7-the-group/1st-semester-project/Hardware/3D_model/Walls_model/walls2.jpg

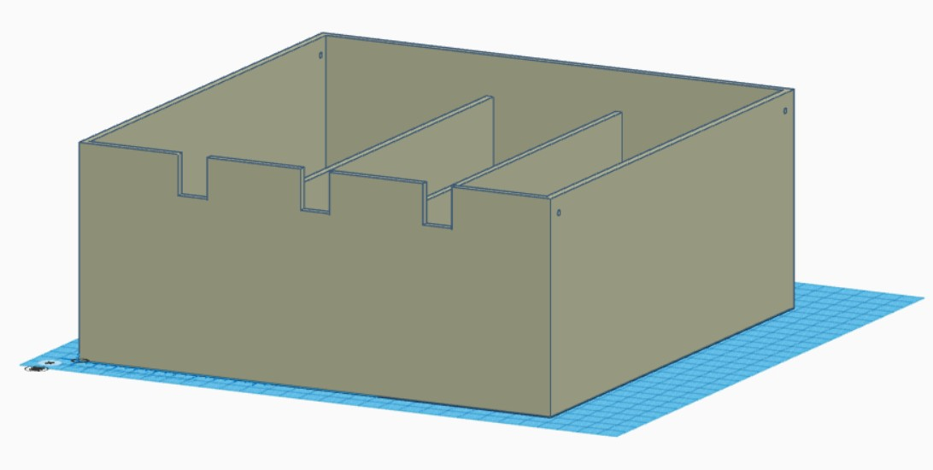
Hardware/3D_model/Walls_model/walls2.jpg
