7-the-group/1st-semester-project/Hardware/Schematic_and_PCB/Control panel (LCD and buttons)/LCD/LCD_sketch.jpg

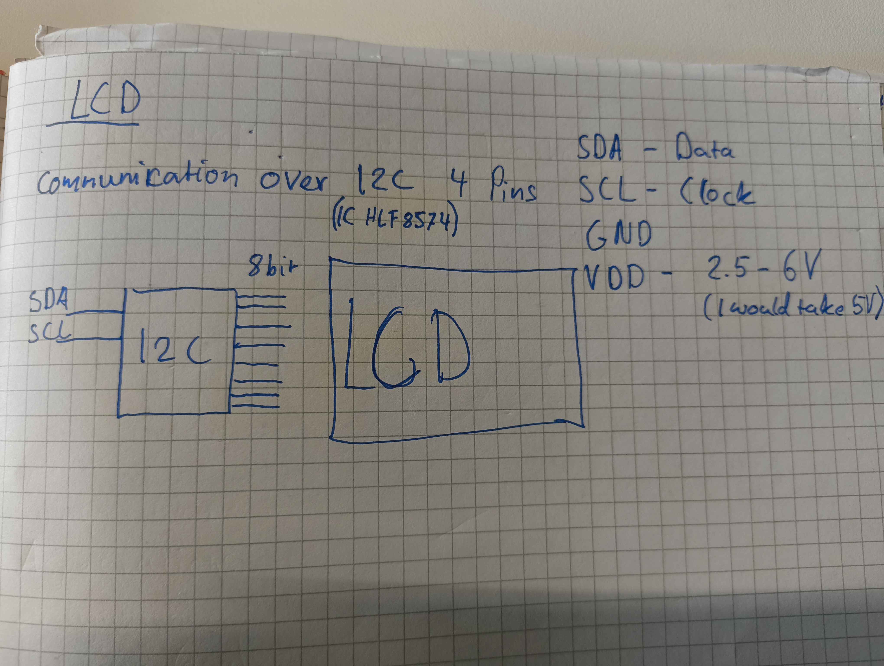
Hardware/Schematic_and_PCB/Control panel (LCD and buttons)/LCD/LCD_sketch.jpg
