7-the-group/1st-semester-project/Hardware/Schematic_and_PCB/LCD_PCB/LCD_PCB_V2.jpg

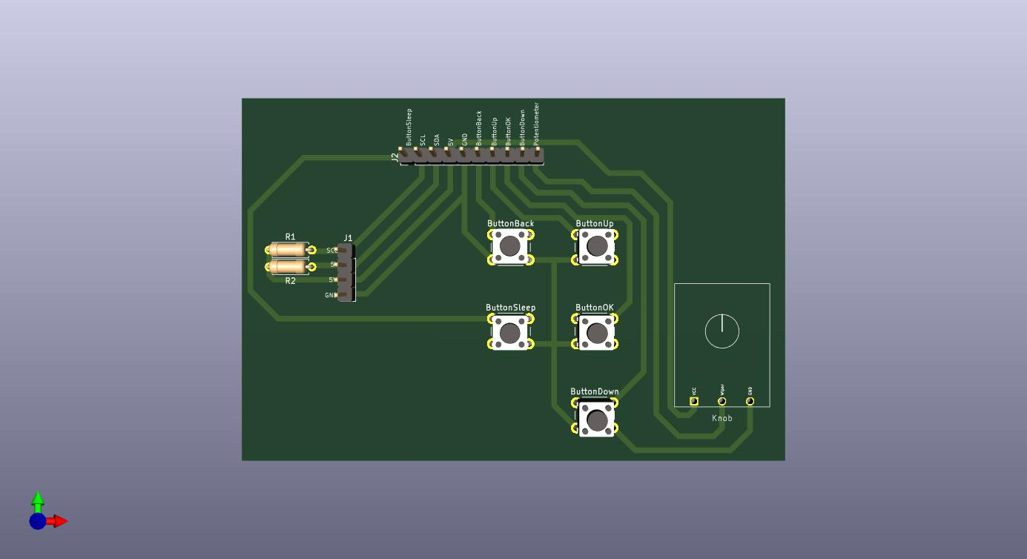
Hardware/Schematic_and_PCB/LCD_PCB/LCD_PCB_V2.jpg
