7-the-group/1st-semester-project/meetings/11-10-2024/meeting_board.jpg

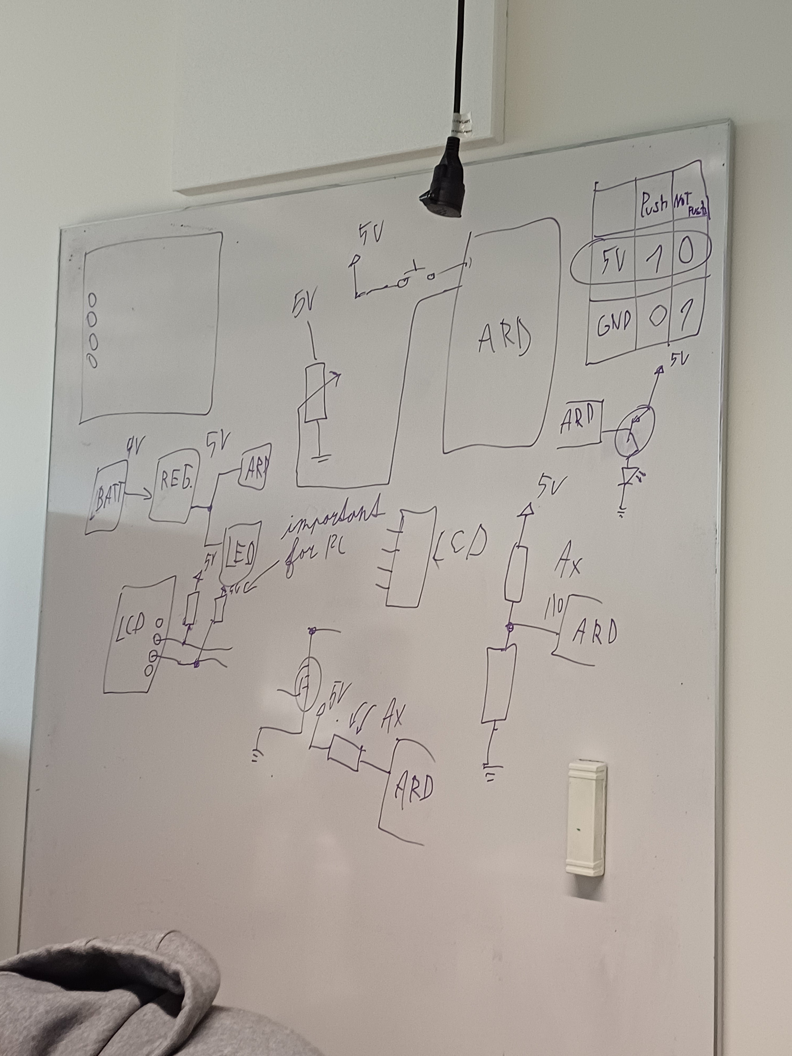
meetings/11-10-2024/meeting_board.jpg
