7-the-group/1st-semester-project/meetings/21-10-2024/sketch_of_the_house.jpeg

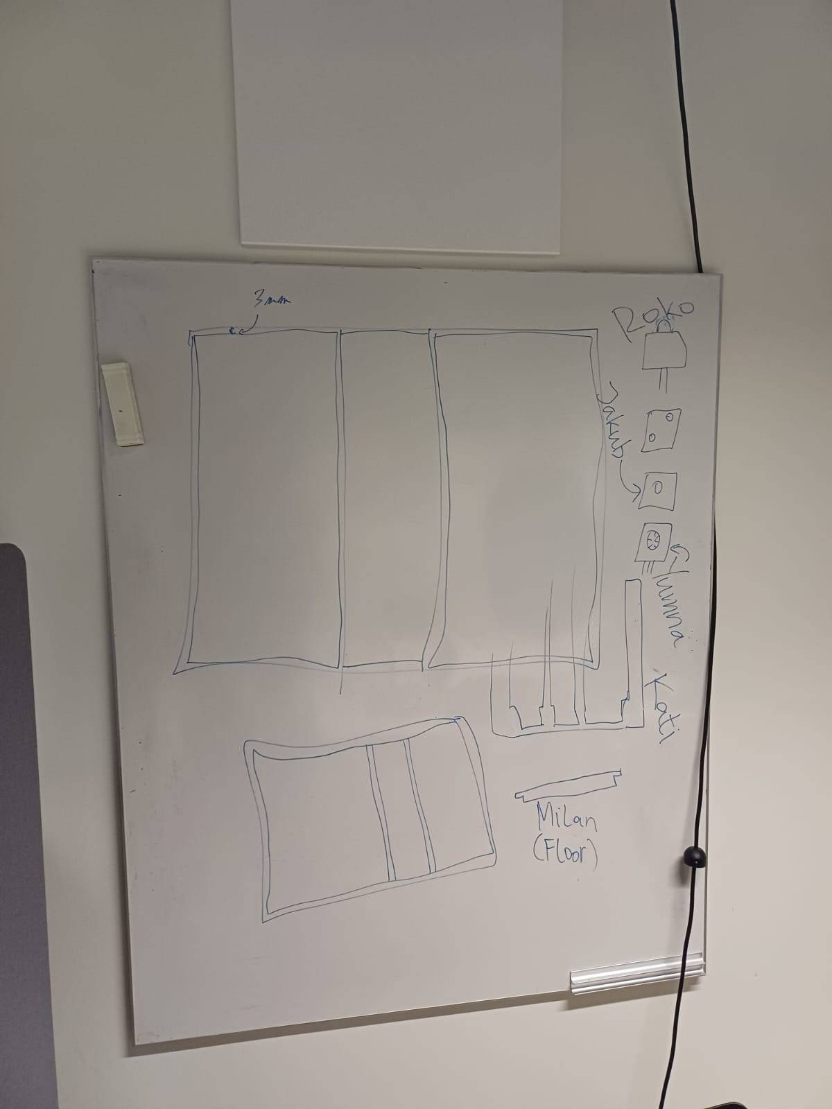
meetings/21-10-2024/sketch_of_the_house.jpeg
