7-the-group/1st-semester-project/meetings/21-10-2024/sketches_of_a_PCB.jpeg

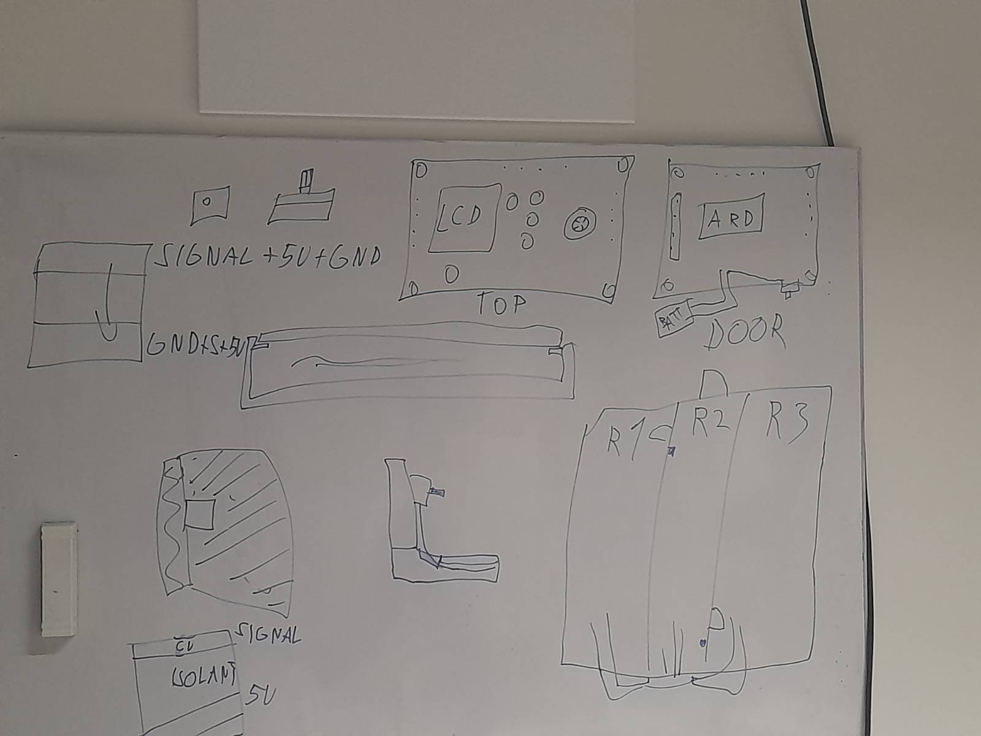
meetings/21-10-2024/sketches_of_a_PCB.jpeg
