7-the-group/1st-semester-project/meetings/21-10-2024/some_sketches.jpeg

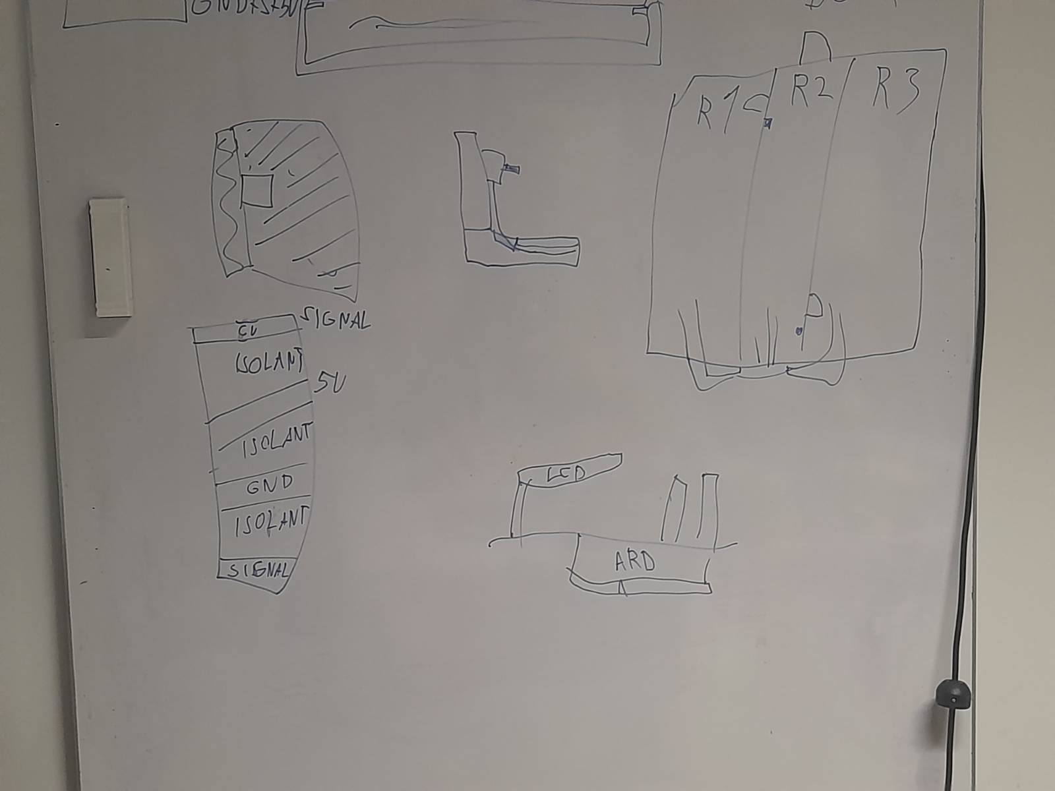
meetings/21-10-2024/some_sketches.jpeg
