7-the-group/1st-semester-project/meetings/26-09-2024/26.09.24_notes.jpg

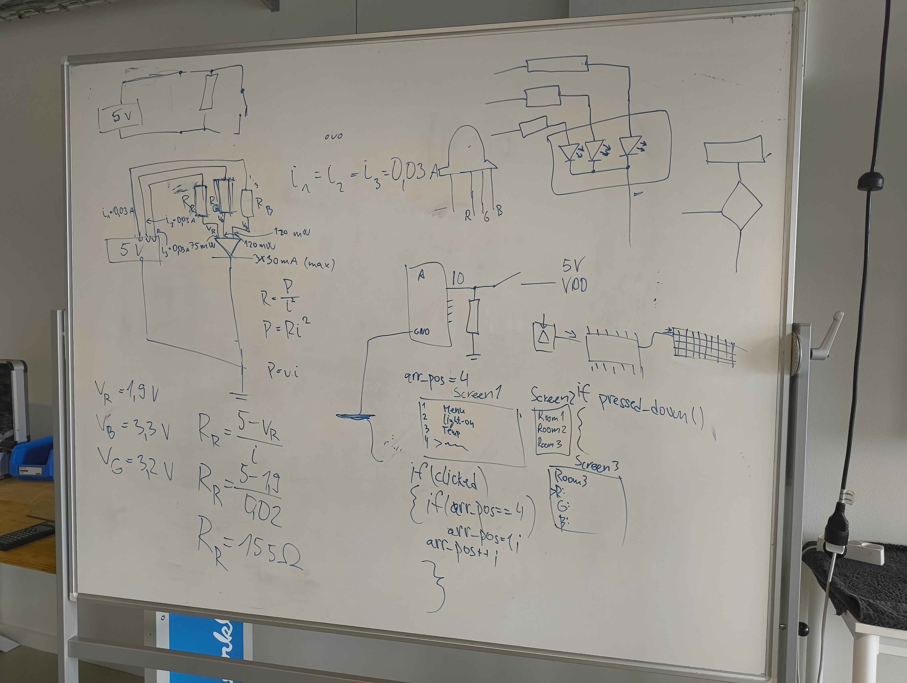
meetings/26-09-2024/26.09.24_notes.jpg
