7-the-group/1st-semester-project/team-identity/GreatPalette.png

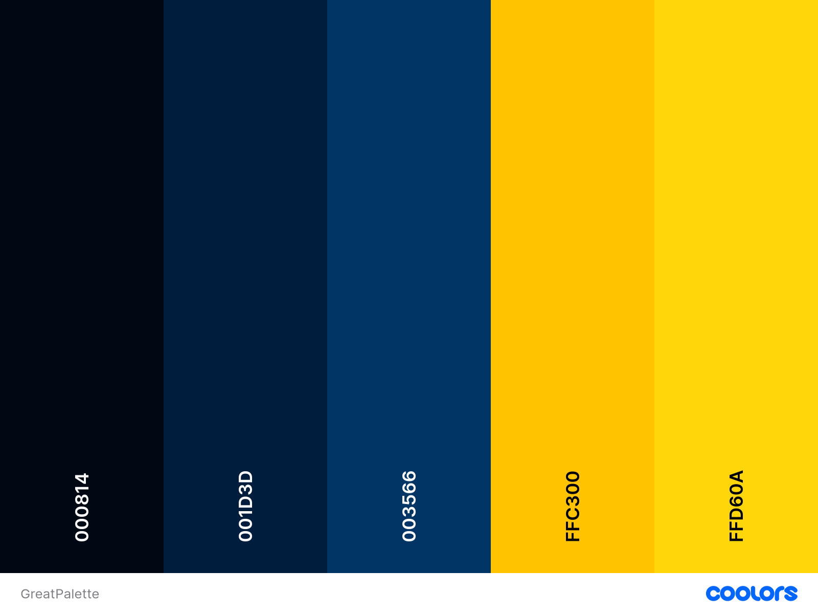
team-identity/GreatPalette.png
