7-the-group/1st-semester-project/Hardware/Room 3/Room3/room3.kicad_sch

## KiCad design Hardware/Room 3/Room3/room3.kicad_sch (2024-10-16)

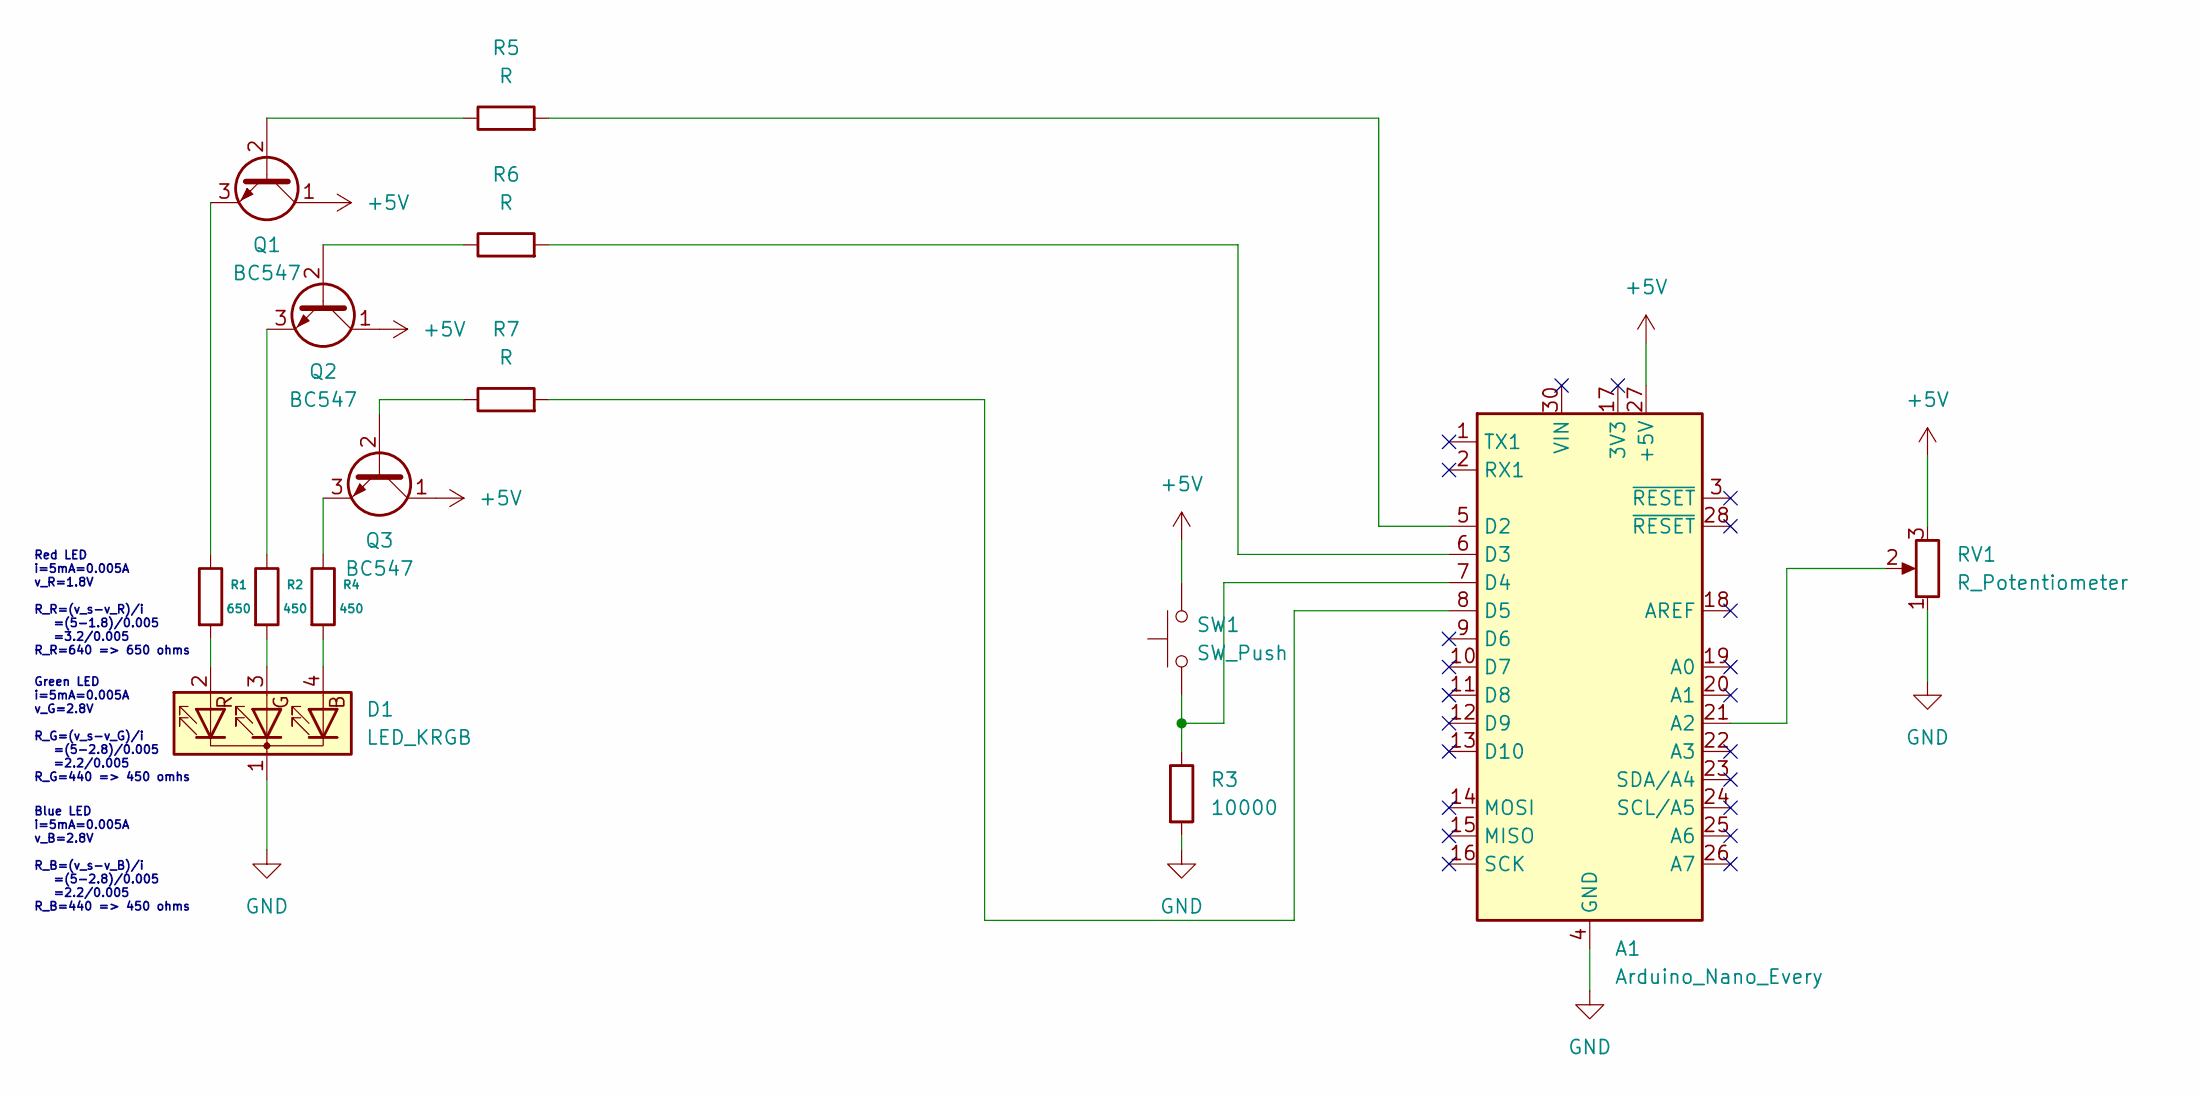
[picture p90: schematic room3.kicad_sch]

Parts:
A1: Arduino_Nano_Every; Arduino_Nano
D1: LED_KRGB
Q1, Q2, Q3: BC547; TO-92_Inline
R1: 650
R2, R4: 450
R3: 10000
R5, R6, R7: R
RV1: R_Potentiometer
SW1: SW_Push

Connections:
+5V: A1.27 (+5V), Q1.1 (C), Q2.1 (C), Q3.1 (C), RV1.3, SW1.2
GND: A1.4 (GND), A1.29 (GND), D1.1 (K), R3.2, RV1.1
unnamed: A1.5 (D2), R5.2
unnamed: A1.6 (D3), R6.2
unnamed: A1.7 (D4), R3.1, SW1.1
unnamed: A1.8 (D5), R7.2
unnamed: A1.21 (A2), RV1.2
unnamed: D1.2 (RA), R1.2
unnamed: D1.3 (GA), R2.2
unnamed: D1.4 (BA), R4.2
unnamed: Q1.2 (B), R5.1
unnamed: Q1.3 (E), R1.1
unnamed: Q2.2 (B), R6.1
unnamed: Q2.3 (E), R2.1
unnamed: Q3.2 (B), R7.1
unnamed: Q3.3 (E), R4.1

Notes on the sheet:
Green LED i=5mA=0.005A v_G=2.8V R_G=(v_s-v_G)/i =(5-2.8)/0.005 =2.2/0.005 R_G=440 => 450 omhs
Red LED i=5mA=0.005A v_R=1.8V R_R=(v_s-v_R)/i =(5-1.8)/0.005 =3.2/0.005 R_R=640 => 650 ohms
Blue LED i=5mA=0.005A v_B=2.8V R_B=(v_s-v_B)/i =(5-2.8)/0.005 =2.2/0.005 R_B=440 => 450 ohms
