7-the-group/1st-semester-project/Hardware/Whole schematic/SmartHomeSchematic/SmartHomeSchematic.kicad_sch

## KiCad design Hardware/Whole schematic/SmartHomeSchematic/SmartHomeSchematic.kicad_sch (2024-11-01)

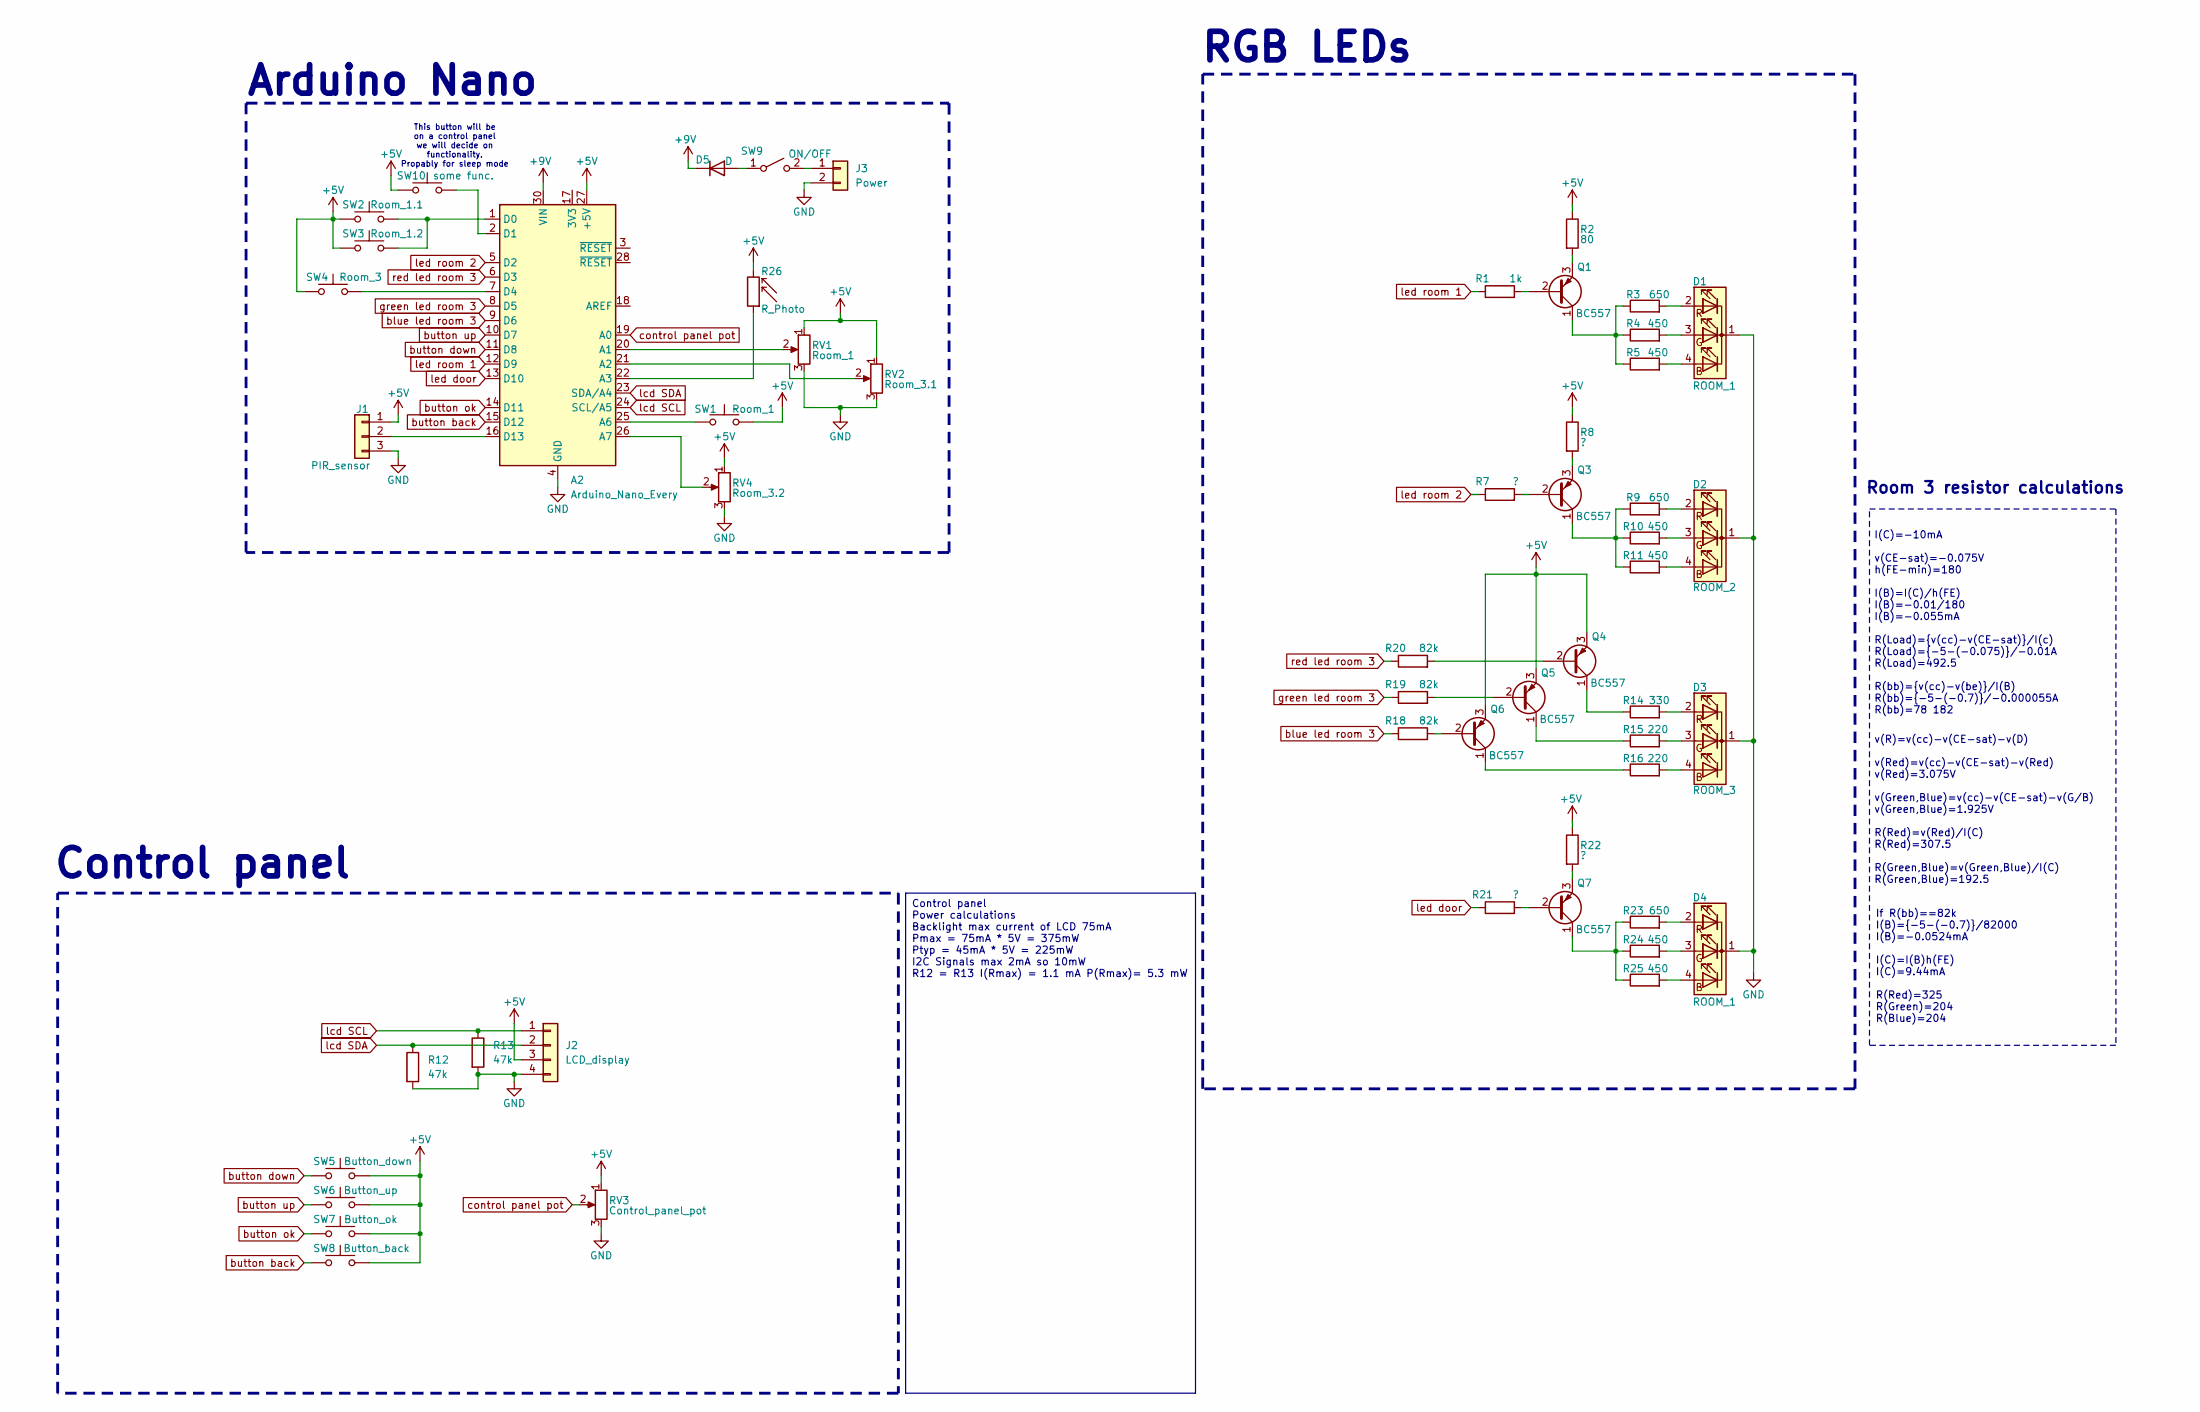
[picture p91: schematic SmartHomeSchematic.kicad_sch]

Parts:
A2: Arduino_Nano_Every; Arduino_Nano
D1, D4: ROOM_1
D2: ROOM_2
D3: ROOM_3
D5: D
J1: PIR_sensor
J2: LCD_display
J3: Power
Q1, Q3, Q4, Q5, Q6, Q7: BC557; TO-92_Inline
R1: 1k
R2: 80
R3, R9, R23: 650
R4, R5, R10, R11, R24, R25: 450
R7, R8, R21, R22: ?
R12, R13: 47k
R14: 330
R15, R16: 220
R18, R19, R20: 82k
R26: R_Photo
RV1: Room_1
RV2: Room_3.1
RV3: Control_panel_pot
RV4: Room_3.2
SW1: Room_1
SW2: Room_1.1
SW3: Room_1.2
SW4: Room_3
SW5: Button_down
SW6: Button_up
SW7: Button_ok
SW8: Button_back
SW9: ON/OFF
SW10: some func.

Connections:
+5V: A2.27 (+5V), J1.1, J2.3, Q4.3 (E), Q5.3 (E), Q6.3 (E), R2.1, R8.1, R22.1, R26.2, RV1.1, RV2.1, RV3.1, RV4.1, SW1.2, SW2.1, SW3.1, SW4.1, SW5.2, SW6.2, SW7.2, SW8.2, SW10.1
+9V: A2.30 (VIN), D5.1 (K)
GND: A2.4 (GND), A2.29 (GND), D1.1 (K), D2.1 (K), D3.1 (K), D4.1 (K), J1.3, J2.4, J3.2, R12.2, R13.2, RV1.3, RV2.3, RV3.3, RV4.3
unnamed: A2.1 (D0), SW2.2, SW3.2
unnamed: A2.2 (D1), SW10.2
unnamed: A2.7 (D4), SW4.2
unnamed: A2.16 (D13), J1.2
unnamed: A2.20 (A1), RV1.2
unnamed: A2.21 (A2), RV2.2
unnamed: A2.22 (A3), R26.1
unnamed: A2.25 (A6), SW1.1
unnamed: A2.26 (A7), RV4.2
unnamed: D1.2 (RA), R3.2
unnamed: D1.3 (GA), R4.2
unnamed: D1.4 (BA), R5.2
unnamed: D2.2 (RA), R9.2
unnamed: D2.3 (GA), R10.2
unnamed: D2.4 (BA), R11.2
unnamed: D3.2 (RA), R14.2
unnamed: D3.3 (GA), R15.2
unnamed: D3.4 (BA), R16.2
unnamed: D4.2 (RA), R23.2
unnamed: D4.3 (GA), R24.2
unnamed: D4.4 (BA), R25.2
unnamed: D5.2 (A), SW9.1 (A)
unnamed: J3.1, SW9.2 (B)
unnamed: Q1.1 (C), R3.1, R4.1, R5.1
unnamed: Q1.2 (B), R1.2
unnamed: Q1.3 (E), R2.2
unnamed: Q3.1 (C), R9.1, R10.1, R11.1
unnamed: Q3.2 (B), R7.2
unnamed: Q3.3 (E), R8.2
unnamed: Q4.1 (C), R14.1
unnamed: Q4.2 (B), R20.2
unnamed: Q5.1 (C), R15.1
unnamed: Q5.2 (B), R19.2
unnamed: Q6.1 (C), R16.1
unnamed: Q6.2 (B), R18.2
unnamed: Q7.1 (C), R23.1, R24.1, R25.1
unnamed: Q7.2 (B), R21.2
unnamed: Q7.3 (E), R22.2
blue led room 3: A2.9 (D6), R18.1
button back: A2.15 (D12), SW8.1
button down: A2.11 (D8), SW5.1
button ok: A2.14 (D11), SW7.1
button up: A2.10 (D7), SW6.1
control panel pot: A2.19 (A0), RV3.2
green led room 3: A2.8 (D5), R19.1
lcd SCL: A2.24 (SCL/A5), J2.1, R13.1
lcd SDA: A2.23 (SDA/A4), J2.2, R12.1
led door: A2.13 (D10), R21.1
led room 1: A2.12 (D9), R1.1
led room 2: A2.5 (D2), R7.1
red led room 3: A2.6 (D3), R20.1

Notes on the sheet:
Control panel Power calculations Backlight max current of LCD 75mA Pmax = 75mA * 5V = 375mW Ptyp = 45mA * 5V = 225mW I2C Signals max 2mA so 10mW R12 = R13 I(Rmax) = 1.1 mA P(Rmax)= 5.3 mW
This button will be on a control panel we will decide on functionality. Propably for sleep mode
If R(bb)==82k I(B)={-5-(-0.7)}/82000 I(B)=-0.0524mA I(C)=I(B)h(FE) I(C)=9.44mA R(Red)=325 R(Green)=204 R(Blue)=204
Room 3 resistor calculations
v(R)=v(cc)-v(CE-sat)-v(D) v(Red)=v(cc)-v(CE-sat)-v(Red) v(Red)=3.075V v(Green,Blue)=v(cc)-v(CE-sat)-v(G/B) v(Green,Blue)=1.925V R(Red)=v(Red)/I(C) R(Red)=307.5 R(Green,Blue)=v(Green,Blue)/I(C) R(Green,Blue)=192.5
Arduino Nano
Control panel
RGB LEDs
I(C)=-10mA v(CE-sat)=-0.075V h(FE-min)=180 I(B)=I(C)/h(FE) I(B)=-0.01/180 I(B)=-0.055mA R(Load)={v(cc)-v(CE-sat)}/I(c) R(Load)={-5-(-0.075)}/-0.01A R(Load)=492.5 R(bb)={v(cc)-v(be)}/I(B) R(bb)={-5-(-0.7)}/-0.000055A R(bb)=78 182
