7-the-group/1st-semester-project/Hardware/Schematic_and_PCB/Control panel (LCD and buttons)/ControlPanel/ControlPanel.kicad_sch

## KiCad design Hardware/Schematic_and_PCB/Control panel (LCD and buttons)/ControlPanel/ControlPanel.kicad_sch (2024-10-17)

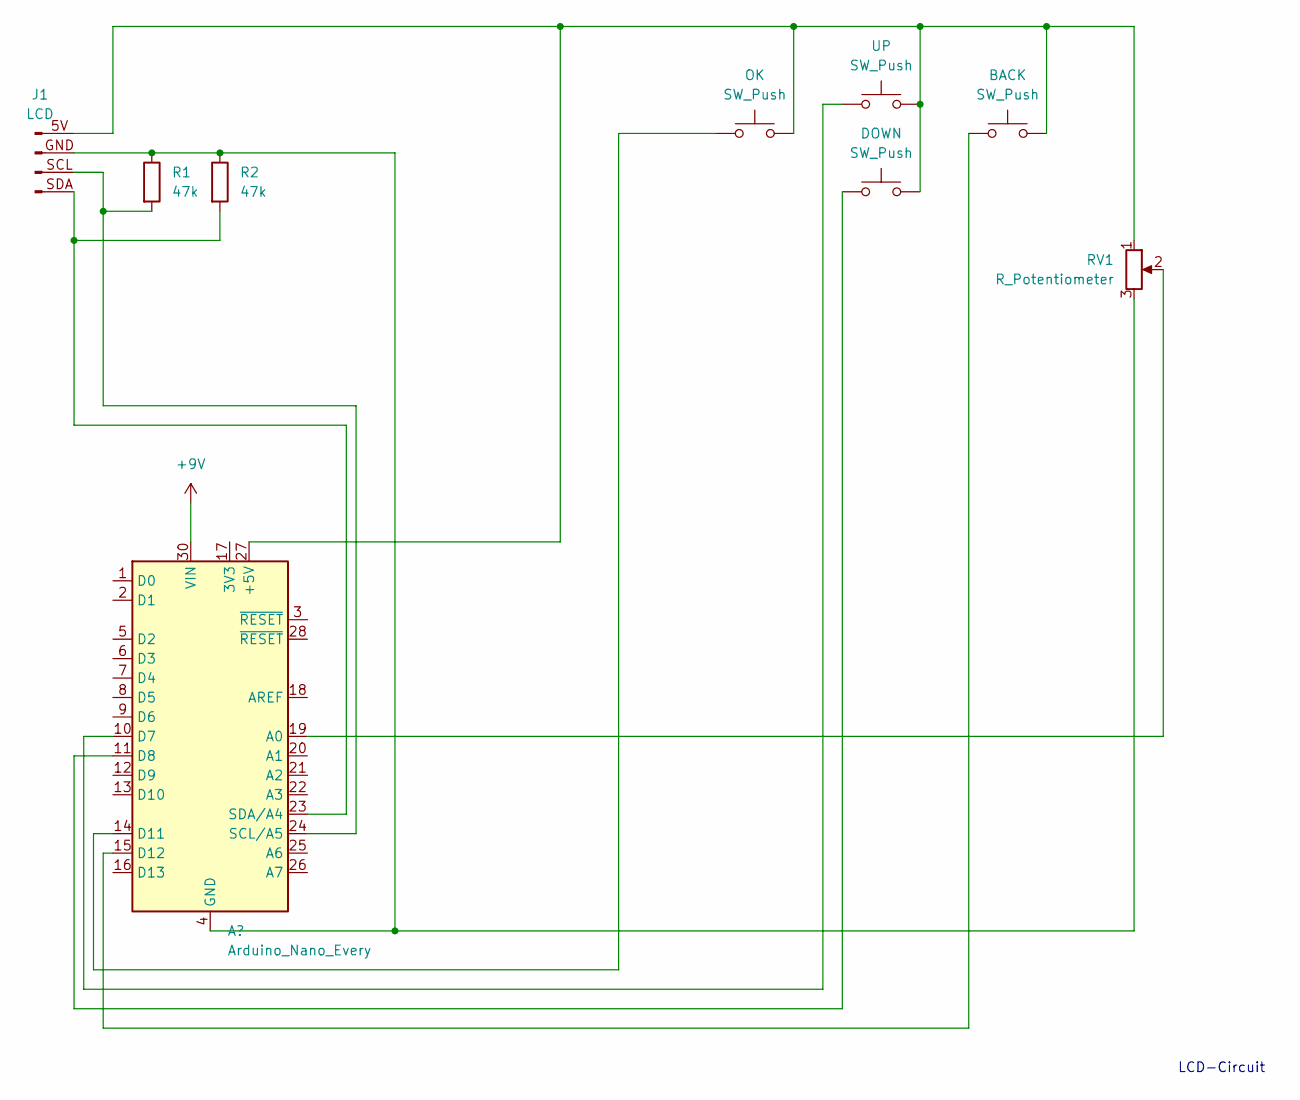
[picture p92: schematic ControlPanel.kicad_sch]

Parts:
A1: Arduino_Nano_Every; Arduino_Nano
BACK: SW_Push; LED_0201_0603Metric
DOWN: SW_Push; LED_0201_0603Metric
J1: LCD
OK: SW_Push; LED_0201_0603Metric
R1, R2: 47k
RV1: R_Potentiometer; BatteryHolder_Keystone_1058_1x2032
UP: SW_Push; LED_0201_0603Metric

Connections:
+9V: A1.30 (VIN)
unnamed: A1.10 (D7), UP.1
unnamed: A1.11 (D8), DOWN.1
unnamed: A1.14 (D11), OK.1
unnamed: A1.15 (D12), BACK.1
unnamed: A1.19 (A0), RV1.2
unnamed: A1.23 (SDA/A4), J1.SDA (Pin_4), R2.2
unnamed: A1.24 (SCL/A5), J1.SCL (Pin_3), R1.2
unnamed: A1.27 (+5V), BACK.2, DOWN.2, J1.5V (Pin_1), OK.2, RV1.1, UP.2
unnamed: A1.4 (GND), A1.29 (GND), J1.GND (Pin_2), R1.1, R2.1, RV1.3

Notes on the sheet:
LCD-Circuit
