7-the-group/1st-semester-project/Hardware/Schematic_and_PCB/Room 1/Room1/Room 1.kicad_sch

## KiCad design Hardware/Schematic_and_PCB/Room 1/Room1/Room 1.kicad_sch (2024-10-21)

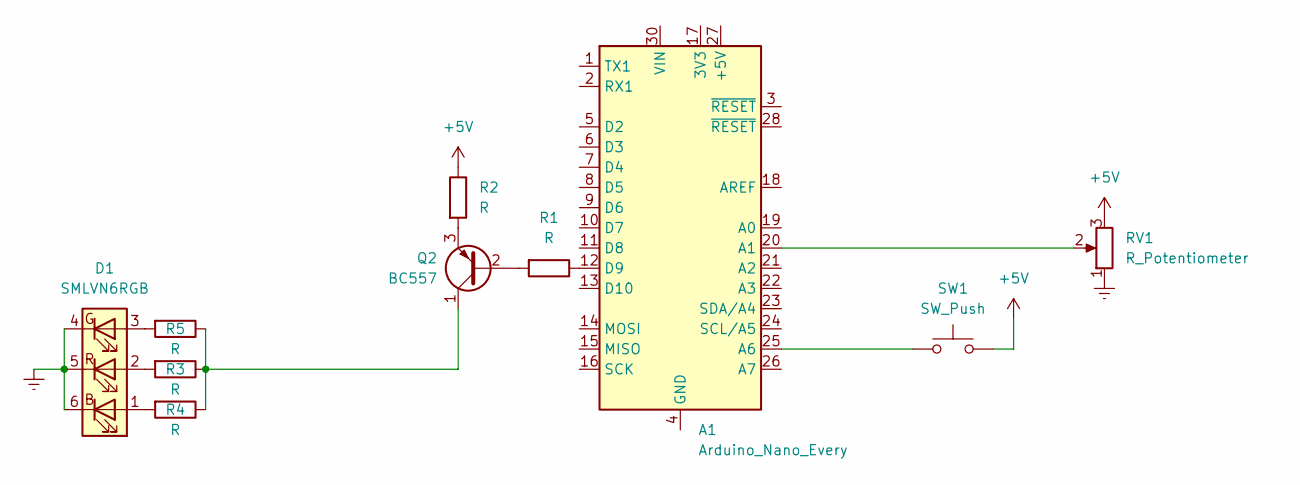
[picture p93: schematic Room 1.kicad_sch]

Parts:
A1: Arduino_Nano_Every; Arduino_Nano
D1: SMLVN6RGB; LED_ROHM_SMLVN6
Q2: BC557; TO-92_Inline
R1, R2, R3, R4, R5: R
RV1: R_Potentiometer
SW1: SW_Push

Connections:
+5V: R2.1, RV1.3, SW1.2
Earth: RV1.1
unnamed: A1.12 (D9), R1.1
unnamed: A1.20 (A1), RV1.2
unnamed: A1.25 (A6), SW1.1
unnamed: A1.4 (GND), A1.29 (GND)
unnamed: D1.1 (BA), R4.2
unnamed: D1.2 (RA), R3.2
unnamed: D1.3 (GA), R5.2
unnamed: Q2.1 (C), R3.1, R4.1, R5.1
unnamed: Q2.2 (B), R1.2
unnamed: Q2.3 (E), R2.2
~: D1.4 (GK), D1.5 (RK), D1.6 (BK)
