7-the-group/1st-semester-project/Hardware/Schematic_and_PCB/Room 2/Room2/Room2.kicad_sch

## KiCad design Hardware/Schematic_and_PCB/Room 2/Room2/Room2.kicad_sch (2024-10-17)

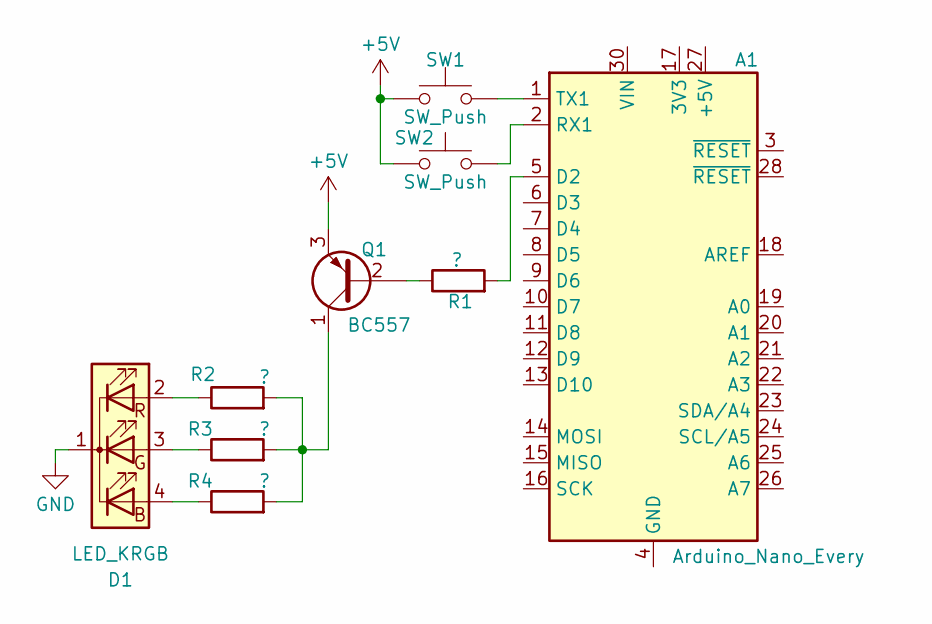
[picture p94: schematic Room2.kicad_sch]

Parts:
A1: Arduino_Nano_Every; Arduino_Nano
D1: LED_KRGB
Q1: BC557; TO-92_Inline
R1, R2, R3, R4: ?
SW1, SW2: SW_Push

Connections:
+5V: Q1.3 (E), SW1.1, SW2.1
GND: D1.1 (K)
unnamed: A1.1 (TX1), SW1.2
unnamed: A1.2 (RX1), SW2.2
unnamed: A1.5 (D2), R1.2
unnamed: A1.4 (GND), A1.29 (GND)
unnamed: D1.2 (RA), R2.1
unnamed: D1.3 (GA), R3.1
unnamed: D1.4 (BA), R4.1
unnamed: Q1.1 (C), R2.2, R3.2, R4.2
unnamed: Q1.2 (B), R1.1
