7-the-group/1st-semester-project/Hardware/Schematic_and_PCB/Room 3/Room3/Room3.kicad_sch

## KiCad design Hardware/Schematic_and_PCB/Room 3/Room3/Room3.kicad_sch (2024-12-05)

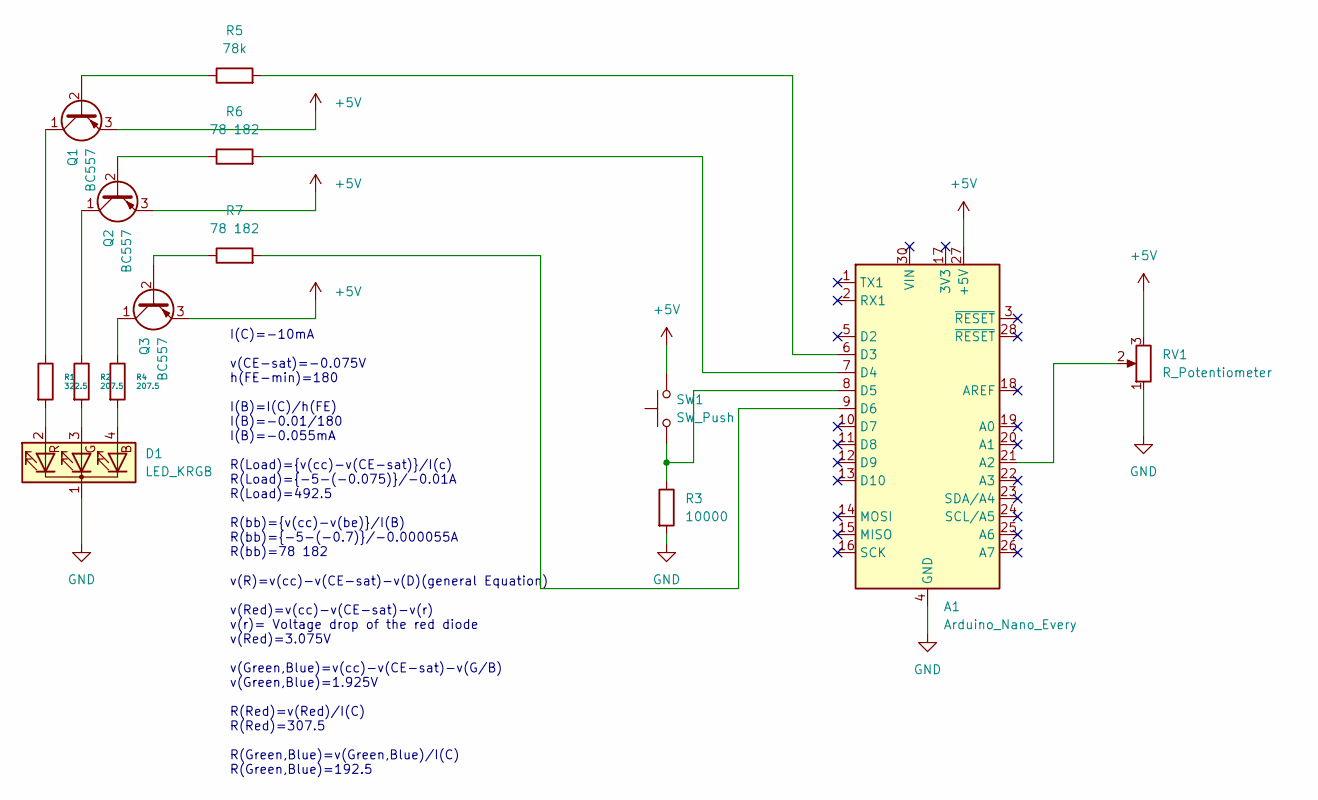
[picture p95: schematic Room3.kicad_sch]

Parts:
A1: Arduino_Nano_Every; Arduino_Nano
D1: LED_KRGB
Q1, Q2, Q3: BC557; TO-92_Inline
R1: 322.5
R2, R4: 207.5
R3: 10000
R5: 78k
R6, R7: 78 182
RV1: R_Potentiometer
SW1: SW_Push

Connections:
+5V: A1.27 (+5V), Q1.3 (E), Q2.3 (E), Q3.3 (E), RV1.3, SW1.2
GND: A1.4 (GND), A1.29 (GND), D1.1 (K), R3.2, RV1.1
unnamed: A1.6 (D3), R5.2
unnamed: A1.7 (D4), R6.2
unnamed: A1.8 (D5), R3.1, SW1.1
unnamed: A1.9 (D6), R7.2
unnamed: A1.21 (A2), RV1.2
unnamed: D1.2 (RA), R1.2
unnamed: D1.3 (GA), R2.2
unnamed: D1.4 (BA), R4.2
unnamed: Q1.1 (C), R1.1
unnamed: Q1.2 (B), R5.1
unnamed: Q2.1 (C), R2.1
unnamed: Q2.2 (B), R6.1
unnamed: Q3.1 (C), R4.1
unnamed: Q3.2 (B), R7.1

Notes on the sheet:
v(R)=v(cc)-v(CE-sat)-v(D)(general Equation) v(Red)=v(cc)-v(CE-sat)-v(r) v(r)= Voltage drop of the red diode v(Red)=3.075V v(Green,Blue)=v(cc)-v(CE-sat)-v(G/B) v(Green,Blue)=1.925V R(Red)=v(Red)/I(C) R(Red)=307.5 R(Green,Blue)=v(Green,Blue)/I(C) R(Green,Blue)=192.5
I(C)=-10mA v(CE-sat)=-0.075V h(FE-min)=180 I(B)=I(C)/h(FE) I(B)=-0.01/180 I(B)=-0.055mA R(Load)={v(cc)-v(CE-sat)}/I(c) R(Load)={-5-(-0.075)}/-0.01A R(Load)=492.5 R(bb)={v(cc)-v(be)}/I(B) R(bb)={-5-(-0.7)}/-0.000055A R(bb)=78 182
