7-the-group/1st-semester-project/Product/Software/include/room_1.h

#ifndef ROOM_1_H_INCLUDED
#define ROOM_1_H_INCLUDED

void init_room_1();
void update_room_1();

void turn_on_light_room_1();
void turn_off_light_room_1();
void switch_light_room_1();
void set_light_intensity_room_1(unsigned char intensity);
int get_light_intensity_room_1();

#endif
